cassm/will-o-the-wisp/teensyFirmware/firmware/fire_palette.h

#ifndef FIRE_PALETTE_H
#define FIRE_PALETTE_H

// RGBW file generated via genPalette.py, created by Cass May

#include <stdint.h>

int firePaletteLen = 750;
const uint16_t fireRgbwPalette[750][4] PROGMEM = {{116, 24, 0, 35}, {122, 14, 0, 47}, {152, 15, 0, 34}, {186, 16, 0, 23}, {195, 17, 0, 17}, {199, 20, 0, 12}, {202, 20, 0, 9}, {208, 20, 0, 6}, {213, 19, 0, 5}, {221, 19, 0, 4}, {226, 20, 0, 2}, {233, 20, 0, 0}, {241, 22, 0, 0}, {251, 24, 0, 0}, {257, 25, 0, 0}, {268, 26, 0, 0}, {276, 28, 0, 0}, {285, 27, 0, 0}, {296, 29, 0, 0}, {305, 31, 0, 0}, {317, 33, 0, 0}, {327, 34, 0, 0}, {341, 36, 0, 0}, {350, 37, 0, 0}, {362, 39, 0, 0}, {373, 40, 0, 0}, {385, 42, 0, 0}, {394, 44, 0, 0}, {409, 45, 0, 0}, {420, 48, 0, 0}, {431, 51, 0, 0}, {438, 53, 0, 0}, {444, 54, 0, 0}, {453, 55, 0, 0}, {460, 57, 0, 0}, {468, 60, 0, 0}, {476, 63, 0, 0}, {486, 64, 0, 0}, {493, 66, 0, 0}, {501, 69, 0, 0}, {508, 72, 0, 0}, {517, 73, 0, 0}, {523, 74, 0, 0}, {531, 76, 0, 0}, {536, 77, 0, 0}, {541, 78, 0, 0}, {546, 79, 0, 1}, {550, 81, 0, 2}, {555, 84, 0, 4}, {560, 84, 0, 4}, {565, 86, 0, 4}, {569, 88, 0, 4}, {574, 88, 0, 4}, {576, 88, 0, 4}, {580, 89, 0, 5}, {586, 92, 0, 5}, {593, 94, 0, 4}, {597, 94, 0, 4}, {600, 93, 0, 5}, {604, 95, 0, 5}, {608, 97, 0, 5}, {613, 97, 0, 5}, {618, 99, 0, 5}, {619, 98, 0, 6}, {623, 99, 0, 6}, {630, 100, 0, 6}, {637, 105, 0, 5}, {642, 109, 0, 5}, {643, 109, 0, 6}, {649, 108, 0, 7}, {652, 107, 0, 7}, {658, 110, 0, 7}, {661, 110, 0, 7}, {666, 113, 0, 6}, {670, 114, 0, 7}, {675, 116, 0, 8}, {679, 118, 0, 8}, {686, 120, 0, 7}, {689, 121, 0, 7}, {693, 123, 0, 7}, {698, 125, 0, 8}, {702, 125, 0, 8}, {709, 125, 0, 8}, {712, 126, 0, 8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

#endif
