cassm/will-o-the-wisp/teensyFirmware/firmware/unicornBarf_palette.h

#ifndef UNICORNBARF_PALETTE_H
#define UNICORNBARF_PALETTE_H

// RGBW file generated via genPalette.py, created by Cass May

#include <stdint.h>

int unicornBarfPaletteLen = 1024;
const uint16_t unicornBarfRgbwPalette[1024][4] PROGMEM = {{667, 0, 45, 355}, {673, 0, 34, 349}, {677, 0, 45, 345}, {678, 0, 41, 344}, {682, 0, 48, 340}, {685, 0, 48, 337}, {686, 0, 48, 336}, {693, 0, 54, 329}, {694, 0, 57, 328}, {698, 0, 64, 324}, {698, 0, 70, 324}, {698, 0, 73, 324}, {698, 0, 80, 324}, {701, 0, 81, 321}, {706, 0, 82, 316}, {707, 0, 84, 315}, {712, 0, 90, 310}, {710, 0, 93, 312}, {714, 0, 100, 308}, {717, 0, 108, 305}, {722, 0, 111, 300}, {723, 0, 120, 299}, {728, 0, 120, 294}, {730, 0, 120, 292}, {734, 0, 120, 288}, {738, 0, 128, 284}, {738, 0, 132, 284}, {738, 0, 140, 284}, {741, 0, 147, 281}, {742, 0, 149, 280}, {749, 0, 158, 273}, {750, 0, 165, 272}, {754, 0, 163, 268}, {754, 0, 173, 268}, {757, 0, 171, 265}, {758, 0, 178, 264}, {762, 0, 187, 260}, {762, 0, 189, 260}, {765, 0, 204, 257}, {766, 0, 208, 256}, {770, 0, 216, 252}, {773, 0, 218, 249}, {774, 0, 225, 248}, {781, 0, 231, 241}, {782, 0, 239, 240}, {786, 0, 240, 236}, {789, 0, 249, 233}, {790, 0, 252, 232}, {794, 0, 260, 228}, {797, 0, 270, 225}, {799, 0, 274, 223}, {802, 0, 284, 220}, {802, 0, 291, 220}, {805, 0, 304, 217}, {807, 0, 314, 215}, {810, 0, 324, 212}, {810, 0, 324, 212}, {813, 0, 333, 209}, {818, 0, 338, 204}, {823, 0, 347, 199}, {826, 0, 357, 196}, {826, 0, 360, 196}, {829, 0, 379, 193}, {831, 0, 383, 191}, {834, 0, 401, 188}, {834, 0, 404, 188}, {837, 0, 423, 185}, {839, 0, 427, 183}, {842, 0, 437, 180}, {845, 0, 447, 177}, {847, 0, 451, 175}, {850, 0, 469, 172}, {853, 0, 474, 169}, 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

#endif
