cassm/will-o-the-wisp/teensyFirmware/firmware/gamma.h

#ifndef GAMMA_H
#define GAMMA_H

#include <stdint.h>
/* 1024-step brightness table: gamma = 2.3 */

const uint8_t gamma_table[1024] = {   0,   0,   0,   0,   0,   0,   0,   0,   0,   0,   0,   0,   0,   0,   0,   0,
                                      0,   0,   0,   0,   0,   0,   0,   0,   0,   0,   0,   0,   0,   0,   0,   0,
                                      0,   0,   0,   0,   0,   0,   0,   0,   0,   0,   0,   0,   0,   0,   0,   0,
                                      0,   0,   0,   0,   0,   0,   0,   0,   0,   0,   0,   0,   0,   0,   0,   0,
                                      0,   0,   0,   0,   0,   1,   1,   1,   1,   1,   1,   1,   1,   1,   1,   1,
                                      1,   1,   1,   1,   1,   1,   1,   1,   1,   1,   1,   1,   1,   1,   1,   1,
                                      1,   1,   1,   1,   1,   1,   1,   1,   1,   1,   1,   1,   1,   1,   2,   2,
                                      2,   2,   2,   2,   2,   2,   2,   2,   2,   2,   2,   2,   2,   2,   2,   2,
                                      2,   2,   2,   2,   2,   2,   2,   2,   2,   3,   3,   3,   3,   3,   3,   3,
                                      3,   3,   3,   3,   3,   3,   3,   3,   3,   3,   3,   3,   3,   3,   3,   4,
                                      4,   4,   4,   4,   4,   4,   4,   4,   4,   4,   4,   4,   4,   4,   4,   4,
                                      4,   5,   5,   5,   5,   5,   5,   5,   5,   5,   5,   5,   5,   5,   5,   5,
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
                                     82,  82,  82,  83,  83,  83,  84,  84,  84,  85,  85,  85,  85,  86,  86,  86,
                                     87,  87,  87,  88,  88,  88,  89,  89,  89,  90,  90,  90,  90,  91,  91,  91,
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
                                   };

#endif
