cassm/will-o-the-wisp/teensyFirmware/firmware/coords.h

#ifndef COORDS_H
#define COORDS_H

#include <math.h>

enum formFactor { DODECAHEDRON, TUBE };

double phis[] = { 0.68068,  0.24435,  6.03884,  5.60250,  0.00000,
1.04720,  1.41372,  1.23918,  0.85521,  0.68068,
1.41372,  2.09439,  2.77507,  2.33874,  1.85005,
4.18879,  4.86947,  4.43313,  3.94444,  3.50811,
5.04400,  5.60250,  5.42797,  4.86947,  4.48550,
6.09120,  0.19198,  0.36652,  0.00000,  5.91666,
0.80285,  1.29154,  1.72787,  0.80285,  0.36652,
1.72788,  1.90241,  2.28638,  2.46091,  2.09439,
2.77510,  3.14159,  3.50810,  3.33360,  2.94960,
3.82230,  4.18880,  4.55530,  4.38080,  3.99680,
4.99164,  5.48033,  5.91666,  5.23599,  4.55531,
3.14159,  2.46091,  2.89725,  3.38594,  3.82227 };

double thetas[] = {0.73304,  1.13446,  1.01229,  0.34907,  0.24435,
0.83776,  0.90757,  1.62316,  1.74533,  1.16937,
0.48869,  0.00000,  5.79449,  5.89921,  0.38397,
6.03884,  5.93412,  5.27089,  5.14872,  5.55015,
0.00000,  1.30900,  2.47837,  3.80482,  4.97419,
1.39626,  1.39626,  1.85005,  2.26893,  2.18166,
2.04204,  2.07694,  2.84489,  2.87979,  2.47837,
1.83260,  0.66323,  5.61996,  4.45059,  3.14159,
5.37561,  5.44543,  5.11381,  4.53786,  4.66003,
4.88692,  4.88692,  4.10152,  4.01426,  4.43314,
3.52557,  2.75762,  2.65290,  3.14159,  3.63028,
3.40339,  3.43830,  4.20624,  4.24115,  3.80482 };

double lantern_r = 1;

double getSphericalX (int index) {
    return lantern_r * sin(phis[index]) * cos(thetas[index]);
}

double getSphericalY (int index) {
    return lantern_r * sin(phis[index]) * sin(thetas[index]);
}

double getSphericalZ (int index) {
    return lantern_r * cos(phis[index]);
}

double getCylindricalX (int index) {
    if (index == 0) {
        return -0.5;
    }

    return ((float)index / 31) - 0.5;
}

#endif
