cassm/will-o-the-wisp/control/colours.py

orange = (97, 255, 0, 76)
bright_orange = (149, 255, 0, 36)
light_orange = (69, 254, 0, 39)
pale_yellow = (255, 230, 0, 108)
bright_yellow = (255, 235, 0, 16)
mint = (255, 0, 123, 1)
lime = (255, 0, 45, 0)
aqua = (202, 0, 215, 255)
sky = (246, 0, 254, 1)
cobalt = (0, 91, 254, 15)
indigo = (0, 147, 255, 0)
imperial_purple = (0, 159, 255, 9)
lilac = (0, 165, 255, 118)
neon_purple = (0, 151, 255, 0)
eye_bleed_pink = (0, 255, 216, 0)
hard_pink = (0, 255, 144, 2)
neon_rose = (0, 255, 100, 7)
crimson = (0, 255, 9, 37)

colours = [orange, bright_orange, light_orange, pale_yellow, bright_yellow, mint, lime, aqua, sky, cobalt, indigo, imperial_purple, lilac, neon_purple, eye_bleed_pink, hard_pink, neon_rose, crimson]
