cassm/will-o-the-wisp/teensyFirmware/firmware/stressTest_palette.h

#ifndef STRESSTEST_PALETTE_H
#define STRESSTEST_PALETTE_H

// RGBW file generated via genPalette.py, created by Cass May

#include <stdint.h>

int stressTestPaletteLen = 1024;
const uint16_t stressTestRgbwPalette[1024][4] PROGMEM = {{677, 701, 0, 277}, {677, 702, 0, 276}, {677, 702, 0, 276}, {677, 701, 0, 276}, {681, 701, 0, 272}, {682, 702, 0, 272}, {682, 702, 0, 272}, {682, 698, 0, 272}, {685, 701, 0, 268}, {689, 701, 0, 268}, {693, 701, 0, 264}, {694, 698, 0, 264}, {698, 698, 0, 260}, {701, 698, 0, 256}, {706, 697, 0, 252}, {714, 697, 0, 248}, {718, 694, 0, 244}, {726, 694, 0, 236}, {734, 694, 0, 232}, {742, 694, 0, 224}, {753, 693, 0, 216}, {758, 689, 0, 212}, {762, 686, 0, 208}, {774, 686, 0, 200}, {782, 686, 0, 192}, {794, 686, 0, 184}, {802, 685, 0, 176}, {806, 682, 0, 172}, {818, 681, 0, 164}, {822, 681, 0, 160}, {826, 677, 0, 156}, {834, 677, 0, 152}, {834, 677, 0, 152}, {834, 677, 0, 152}, {834, 677, 0, 152}, {834, 678, 0, 152}, {826, 678, 0, 156}, {822, 678, 0, 160}, {818, 681, 0, 164}, {814, 681, 0, 168}, {802, 682, 0, 176}, {794, 682, 0, 184}, {786, 685, 0, 188}, {782, 686, 0, 192}, {774, 690, 0, 200}, {762, 690, 0, 208}, {754, 690, 0, 216}, {742, 690, 0, 224}, {737, 693, 0, 228}, {726, 694, 0, 236}, {721, 697, 0, 240}, {714, 694, 0, 248}, {710, 698, 0, 252}, {702, 698, 0, 256}, {698, 698, 0, 260}, {697, 701, 0, 260}, {694, 701, 0, 264}, {690, 698, 0, 268}, {686, 701, 0, 268}, {686, 702, 0, 268}, {682, 698, 0, 272}, {682, 698, 0, 272}, {682, 698, 0, 272}, {682, 698, 0, 272}, {686, 702, 0, 268}, {686, 702, 0, 268}, {689, 698, 0, 268}, {693, 701, 0, 264}, {694, 698, 0, 264}, {697, 698, 0, 260}, {701, 698, 0, 256}, {706, 698, 0, 252}, {71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

#endif
