cassm/will-o-the-wisp/teensyFirmware/testing_firmware/paletteViewer/unicornBarf_palette.h

#ifndef UNICORNBARF_PALETTE_H
#define UNICORNBARF_PALETTE_H

// RGBW file generated via genPalette.py, created by Cass May

#include <stdint.h>

int unicornBarfPaletteLen = 500;
uint16_t unicornBarfPalette[500][4] = {{586, 0, 115, 436}, {606, 0, 104, 417}, {609, 0, 108, 414}, {618, 0, 117, 404}, {628, 0, 121, 395}, {634, 0, 131, 388}, {634, 0, 136, 388}, {637, 0, 147, 385}, {644, 0, 149, 378}, {647, 0, 154, 375}, {657, 0, 169, 366}, {663, 0, 182, 359}, {669, 0, 181, 353}, {682, 0, 185, 340}, {682, 0, 199, 340}, {686, 0, 203, 337}, {695, 0, 218, 327}, {701, 0, 231, 321}, {705, 0, 232, 318}, {711, 0, 240, 311}, {714, 0, 256, 308}, {724, 0, 274, 298}, {733, 0, 287, 289}, {743, 0, 295, 280}, {749, 0, 308, 273}, {753, 0, 315, 270}, {759, 0, 335, 263}, {762, 0, 353, 260}, {769, 0, 369, 254}, {775, 0, 375, 247}, {788, 0, 395, 235}, {791, 0, 416, 232}, {797, 0, 438, 225}, {800, 0, 459, 222}, {807, 0, 474, 215}, {810, 0, 482, 212}, {819, 0, 504, 203}, {826, 0, 526, 196}, {829, 0, 547, 193}, {833, 0, 574, 188}, {830, 0, 599, 188}, {830, 0, 612, 184}, {825, 0, 662, 182}, {829, 0, 675, 177}, {806, 0, 676, 190}, {798, 0, 704, 193}, {804, 0, 731, 185}, {804, 0, 763, 180}, {796, 0, 784, 182}, {781, 0, 806, 188}, {778, 0, 826, 185}, {750, 0, 837, 191}, {724, 0, 841, 195}, {691, 0, 837, 201}, {660, 0, 839, 201}, {638, 0, 844, 203}, {601, 0, 841, 211}, {574, 0, 832, 222}, {548, 0, 833, 227}, {518, 0, 835, 229}, {496, 0, 834, 233}, {465, 0, 821, 249}, {452, 0, 821, 249}, {452, 0, 821, 249}, {452, 0, 821, 249}, {452, 0, 821, 249}, {452, 0, 821, 249}, {452, 0, 821, 249}, {452, 0, 821, 249}, {452, 0, 821, 249}, {452, 0, 821, 249}, {452, 0, 821, 249}, {452, 0, 821, 249}, {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
 0, 731}, {2, 385, 0, 763}, {0, 391, 21, 755}, {0, 393, 38, 753}, {0, 395, 56, 750}, {0, 397, 76, 747}, {0, 403, 100, 741}, {0, 407, 114, 736}, {0, 414, 136, 728}, {0, 416, 169, 725}, {0, 424, 189, 716}, {0, 433, 209, 705}, {0, 431, 231, 708}, {0, 435, 257, 702}, {0, 437, 276, 700}, {0, 442, 298, 694}, {0, 444, 317, 692}, {0, 446, 342, 689}, {0, 446, 364, 689}, {0, 455, 385, 678}, {0, 457, 405, 676}, {0, 462, 433, 670}, {0, 462, 454, 670}, {0, 466, 498, 665}, {0, 475, 568, 654}, {0, 475, 568, 654}, {0, 475, 568, 654}, {0, 475, 568, 654}, {0, 475, 568, 654}, {0, 475, 568, 654}, {0, 487, 573, 641}, {0, 490, 573, 631}, {0, 459, 542, 642}, {0, 394, 487, 669}, {0, 324, 433, 700}, {0, 262, 377, 728}, {0, 197, 320, 755}, {0, 134, 266, 781}, {0, 69, 209, 811}, {0, 7, 154, 837}, {69, 0, 146, 795}, {143, 0, 142, 749}, {224, 0, 138, 697}, {301, 0, 133, 645}, {379, 0, 125, 596}, {461, 0, 126, 545}, {513, 0, 126, 510}, {526, 0, 113, 497}, {545, 0, 115, 478}, {561, 0, 123, 462}};

#endif
